aalonsopuig/SEN100T/SEN100T_Media/IMG_5899.JPG

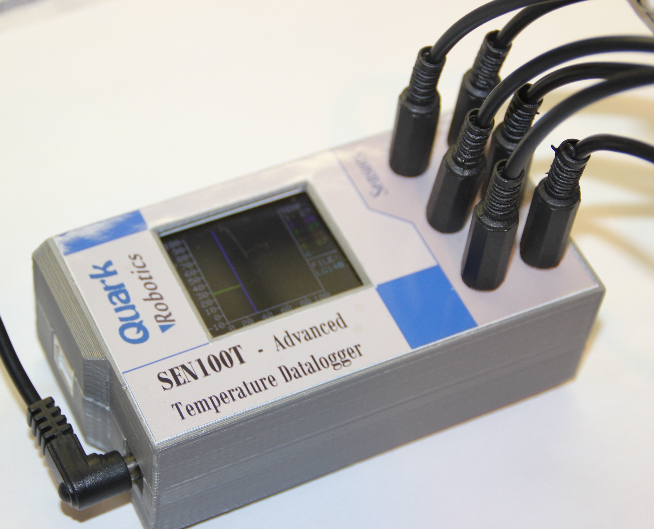
SEN100T_Media/IMG_5899.JPG
