aalonsopuig/SEN100T/SEN100T_Media/IMG_5904.JPG

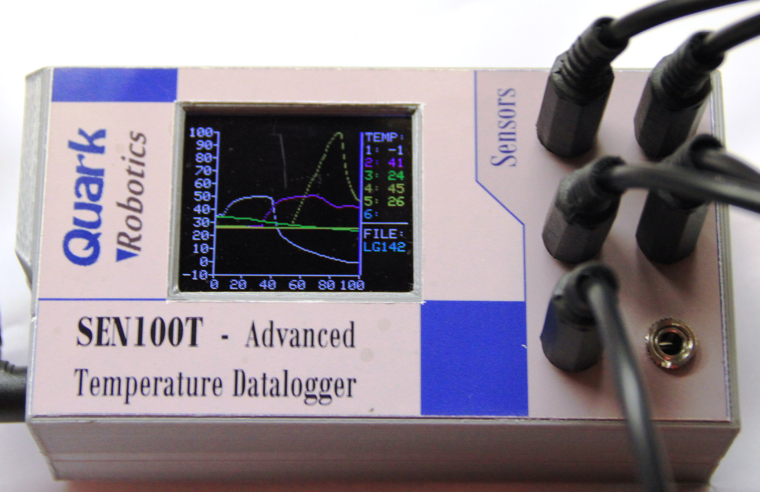
SEN100T_Media/IMG_5904.JPG
