aalonsopuig/SEN100T/SEN100T_Media/IMG_5916.JPG

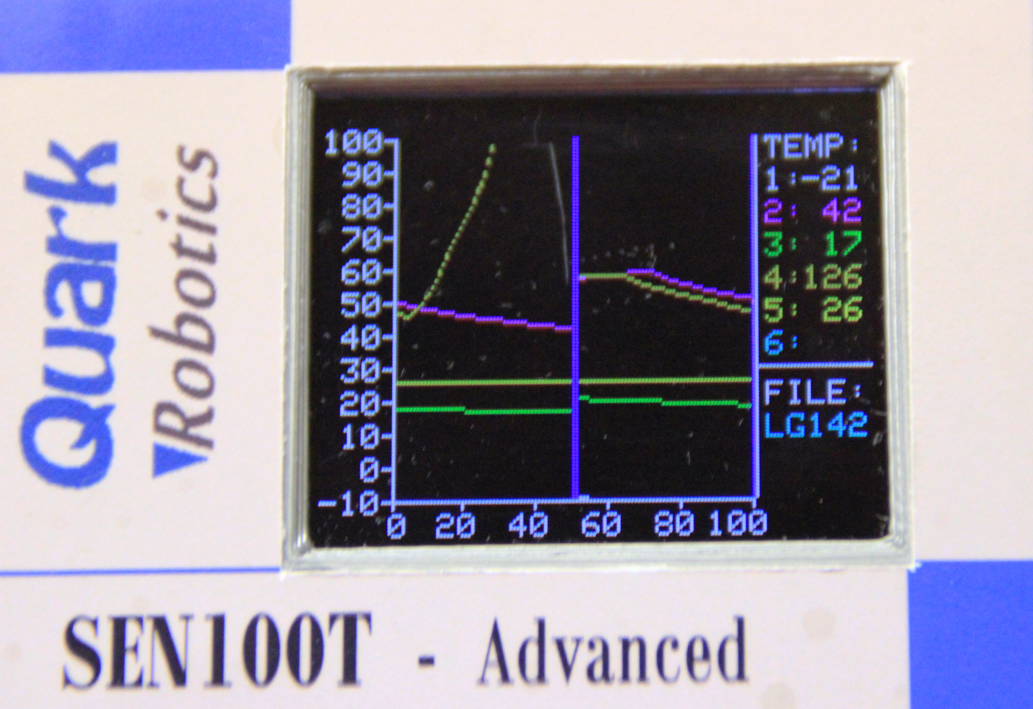
SEN100T_Media/IMG_5916.JPG
